ossanaTomas/CattleTracking_EmbeddedSystemsProyect/dashboard-app/images/dashboard3.png

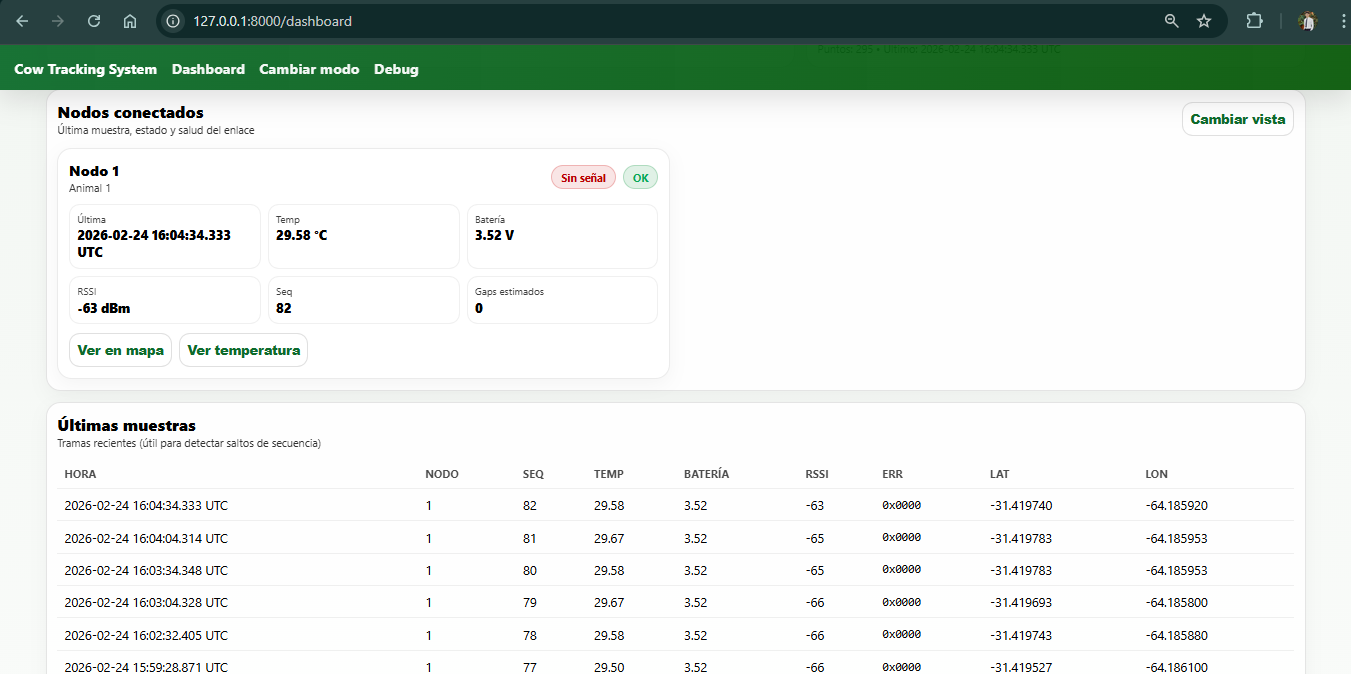
dashboard-app/images/dashboard3.png
