ossanaTomas/CattleTracking_EmbeddedSystemsProyect/dashboard-app/images/dashboard5.png

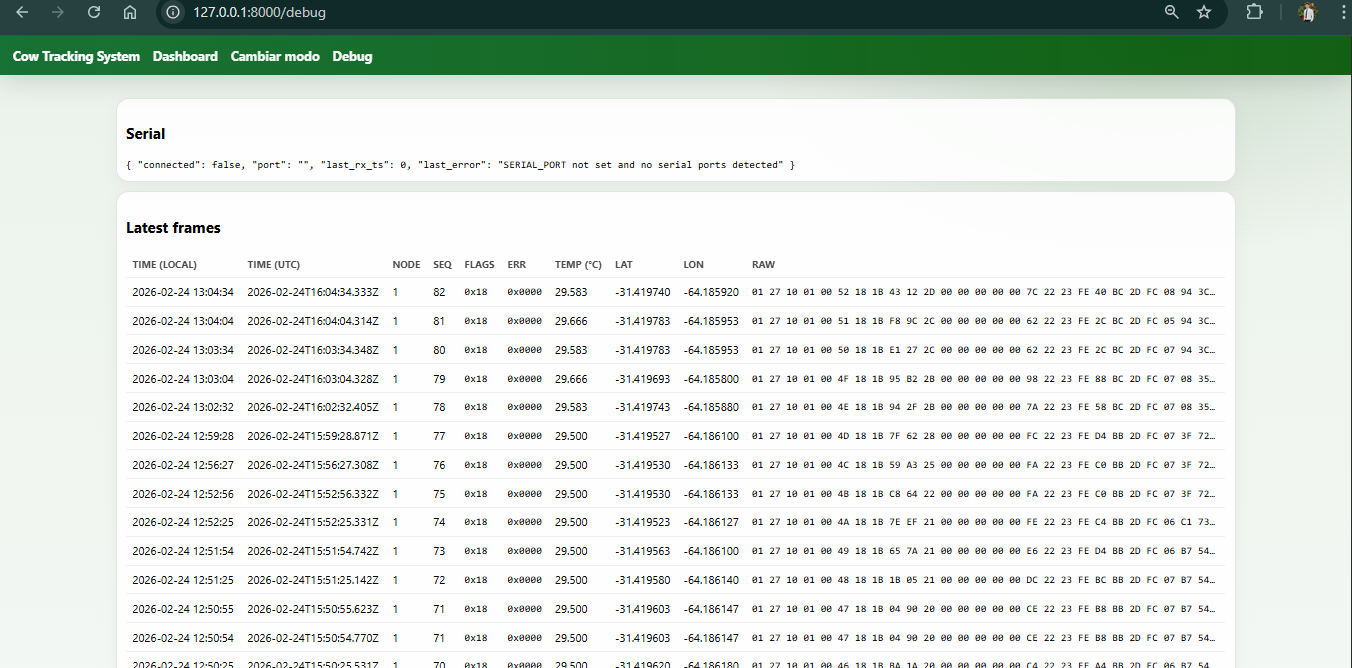
dashboard-app/images/dashboard5.png
