ossanaTomas/CattleTracking_EmbeddedSystemsProyect/firmware/firmware-tracker/Core/Src/OneWire.c

#include "OneWire.h"
#include "stm32f1xx_hal.h"
#include "stdio.h"
#include "string.h"
volatile uint8_t recvFlag;
volatile uint16_t rc_buffer[5];
int8_t Tempi[2];
/**
    @author Stanislav Lakhtin
    @date   11.07.2016
    @brief      @brief Implementación del protocolo 1wire basado en la biblioteca libopencm3 para el microcontrolador STM32F103
 	 	 	 	 	 	Quizás la biblioteca funcione correctamente en otros Reino Unido (se requiere verificación).
 	 	 	 	 	 	Es necesario realizar una verificación para garantizar que la configuración de UART/USART sea correcta para el funcionamiento.
 	 	 	 	 	 	en modo semidúplex
 	 	 	 	 	 	La idea general es utilizar hardware USART uK para simular el funcionamiento con 1 cable.
 	 	 	 	 	 	Los dispositivos se conectan al USART seleccionado al pin TX, que debe estar conectado a la línea
 	 	 	 	 	 	de alimentación con una resistencia de 4,7K.
 	 	 	 	 	 	La implementación de la biblioteca corta RX a TX dentro del Reino Unido, dejando el pin RX disponible para su uso en otras tareas.
 	 	 	 	 	 	La implementación de la biblioteca supone un posible trabajo simultáneo con ambos buses independientes y todos a la vez.
 	 	 	 	 	 	posible UART/USART en el microcontrolador. En este caso, todos los autobuses (hasta 5 unidades) serán abordados y
 	 	 	 	 	 	encuestados individualmente.
 */


extern UART_HandleTypeDef huart2;
#define ow_uart huart2
#define OW_USART USART2
#define MAXDEVICES_ON_THE_BUS 1  // cambio por uno

/*********************************************************************************************/
float Temp[MAXDEVICES_ON_THE_BUS];

uint8_t devices;
OneWire ow;
uint32_t pDelay = 300, i;
uint8_t sensor;

Temperature t;

DEVInfo devInfo;


char *crcOK;

uint16_t USART_ReceiveData(USART_TypeDef* USARTx)
{
	/* Check the parameters */
	assert_param(IS_USART_ALL_PERIPH(USARTx));

	/* Receive Data */
	return (uint16_t)(USARTx->DR & (uint16_t)0x01FF);
}

void USART_SendData(USART_TypeDef* USARTx, uint16_t Data)
{
	/* Check the parameters */
	assert_param(IS_USART_ALL_PERIPH(USARTx));
	assert_param(IS_USART_DATA(Data));

	/* Transmit Data */
	USARTx->DR = (Data & (uint16_t)0x01FF);
}


uint8_t getUsartIndex(void);

void usart_setup(uint32_t baud) {

	ow_uart.Instance = OW_USART;
	ow_uart.Init.BaudRate = baud;
	ow_uart.Init.WordLength = UART_WORDLENGTH_8B;
	ow_uart.Init.StopBits = UART_STOPBITS_1;
	ow_uart.Init.Parity = UART_PARITY_NONE;
	ow_uart.Init.Mode = UART_MODE_TX_RX;
	ow_uart.Init.HwFlowCtl = UART_HWCONTROL_NONE;
	ow_uart.Init.OverSampling = UART_OVERSAMPLING_16;
	if (HAL_HalfDuplex_Init(&ow_uart) != HAL_OK)
	{
		//	    Error_Handler();
		__asm__("NOP");
	}

	__HAL_UART_ENABLE_IT(&ow_uart, UART_IT_RXNE);
}

void owInit(OneWire *ow) {
	int i=0, k = 0;
	for (; i < MAXDEVICES_ON_THE_BUS; i++) {
		uint8_t *r = (uint8_t *)&ow->ids[i];
		k=0;
		for (; k < 8; k++)
			r[k] = 0;
	}
	k=0;
	for (; k < 8; k++)
		ow->lastROM[k] = 0x00;
	ow->lastDiscrepancy = 64;

}

void owReadHandler() { //controlador de interrupciones USART
	uint8_t index = getUsartIndex();
	/*Comprueba que hemos provocado una interrupción debido a RXNE. */
	if (((OW_USART->CR1 & USART_CR1_RXNEIE) != 0) &&
			((OW_USART->SR & UART_FLAG_RXNE) != (uint16_t)RESET)) {

		/* Recibir datos de la periferia y restablecer la bandera*/
		while ((OW_USART->SR & UART_FLAG_RXNE) == (uint16_t)RESET){;}
		rc_buffer[index] = USART_ReceiveData(OW_USART);
		recvFlag &= ~(1 << index);//restablecer la respuesta del indicador recibida después
	}
}

/** Реализация RESET на шине 1wire
 *
 * @param N usart -- выбранный для реализации 1wire usart
 * @return Возвращает 1 если на шине кто-то есть и 0 в противном случае
 */

uint16_t owResetCmd() {
	uint16_t owPresence;

	usart_setup(9600);

	owSend(0xF0); // Send RESET отправляем импуль сброса
	owPresence = owEchoRead(); // Ждём PRESENCE на шине и вовзращаем, что есть

	usart_setup(115200);// перенастраиваем скорость UART
	return owPresence;
}

uint8_t getUsartIndex() {// смотрит по номеру UART c каким будет идти работа
	//	uint8_t result;
	//	if(OW_USART==USART1)result = 0;
	//	else if (OW_USART==USART2)result = 1;
	//	else if (OW_USART==USART3)result = 2;
	return 0;
}

void owSend(uint16_t data) {
	recvFlag |= (1 << getUsartIndex());//устанавливаем флаг если попадем в обработчик прерывания там он сбросится
	USART_SendData(OW_USART, data);//отправляем данные
	while(__HAL_UART_GET_FLAG(&ow_uart, UART_FLAG_TC) == RESET);//ждем пока передача закончится
}

uint8_t owReadSlot(uint16_t data) {//читаем у нас пришла единица или ноль в ответ
	return (data == OW_READ) ? 1 : 0; //если пришло 0xFF, то бит = 1, что то другое бит = 0
}

uint16_t owEchoRead() {//
	uint8_t i = getUsartIndex();//получаем номер USART
	uint16_t pause = 1000;
	while (recvFlag & (1 << i) && pause--);// ждем пока кто-то не ответит но не больше паузы
	return rc_buffer[i];//в зависимости от используемого номера UART
}

uint8_t *byteToBits(uint8_t ow_byte, uint8_t *bits) {//разлагаем 1 байт на 8 байт ,кодируем так скасказать в посылку для 1wire
	uint8_t i;
	for (i = 0; i < 8; i++) {
		if (ow_byte & 0x01) {//если текущий бит в байте ==1 то
			*bits = WIRE_1; //заменяем на число которое при передаче по USART для 1wire будет единцией t.e 0xFF
		} else {
			*bits = WIRE_0;// тоже самое только для 0
		}
		bits++;
		ow_byte = ow_byte >> 1; //сдвигаем обработанный бит
	}
	return bits; //возвращае массив для передачи
}

/**
 * Метод пересылает последовательно 8 байт по одному на каждый бит в data
 * @param usart -- выбранный для эмуляции 1wire UART
 * @param d -- данные
 */
void owSendByte(uint8_t d) {
	uint8_t data[8];
	int i;
	byteToBits(d, data);//преобразовываем байт в биты "массив байт для  передачи UART и эмуляции 1WIRE"
	for (i = 0; i < 8; ++i) {
		owSend(data[i]);
	}
}


uint8_t bitsToByte(uint8_t *bits) {//принимает "кодированый" массив байт полученный по UART и делает из него байт))
	uint8_t target_byte, i;
	target_byte = 0;
	for (i = 0; i < 8; i++) {
		target_byte = target_byte >> 1;
		if (*bits == WIRE_1) {//если пришло  по USART 0xFF то это у нас пришла 1ца
			target_byte |= 0x80;//устанавливаем в 1 старший бит
		}
		bits++;//передвигаемся к следующему байту который является либо 0=0x00 или 1=0xFF
	}
	return target_byte; //возвращаем полученный байт
}

/* Подсчет CRC8 массива mas длиной Len */
uint8_t owCRC(uint8_t *mas, uint8_t Len) {
	uint8_t i, dat, crc, fb, st_byt;
	st_byt = 0;
	crc = 0;
	do {
		dat = mas[st_byt];
		for (i = 0; i < 8; i++) {  // счетчик битов в байте
			fb = crc ^ dat;
			fb &= 1;
			crc >>= 1;
			dat >>= 1;
			if (fb == 1) crc ^= 0x8c; // полином
		}
		st_byt++;
	} while (st_byt < Len); // счетчик байтов в массиве
	return crc;
}

uint8_t owCRC8(RomCode *rom){
	return owCRC((uint8_t*)rom, 7);
}

/*
 * return 1 if has got one more address
 * return 0 if hasn't
 * return -1 if error reading happened
 *
 * переделать на функции обратного вызова для реакции на ошибки
 */
int hasNextRom(OneWire *ow, uint8_t *ROM) {//
	uint8_t ui32BitNumber = 0;
	int zeroFork = -1;
	uint8_t i = 0;
	if (owResetCmd() == ONEWIRE_NOBODY) { //есть ли кто на шине
		return 0;
	}
	owSendByte(ONEWIRE_SEARCH);//
	do {
		uint8_t answerBit =0;
		int byteNum = ui32BitNumber / 8;
		uint8_t *current = (ROM) + byteNum;
		uint8_t cB, cmp_cB, searchDirection = 0;
		owSend(OW_READ); // чтение прямого бита
		cB = owReadSlot(owEchoRead());//ответ от датчика
		owSend(OW_READ); // чтение инверсного бита
		cmp_cB = owReadSlot(owEchoRead());//ответ от датчика
		if (cB == cmp_cB && cB == 1)//сравниваем два ответа
			return -1;//ошибка никто не ответил
		if (cB != cmp_cB) { //нормальная ситуация пришло либо 10 либо 01
			searchDirection = cB;//выбираем в каком направлении будем двигатся дальше
		} else {//колизия пришло 00 т.е текущий бит у ROM-ов разный
			if (ui32BitNumber == ow->lastDiscrepancy)//если текущая позиция колизии равна прошлой
				searchDirection = 1;//выбираем в каком направлении будем двигатся дальше
			else {
				if (ui32BitNumber > ow->lastDiscrepancy) {//если мы зашили дальше
					searchDirection = 0;//выбираем в каком направлении будем двигатся дальше
				} else {
					searchDirection = (uint8_t) ((ow->lastROM[byteNum] >> ui32BitNumber % 8) & 0x01);
				}
				if (searchDirection == 0)
					zeroFork = ui32BitNumber;//запоминаем развилку
			}
		}
		// сохраняем бит
		if (searchDirection)
			*(current) |= 1 << ui32BitNumber % 8;//выставляем бит в текущем байте байте
		answerBit = (uint8_t) ((searchDirection == 0) ? WIRE_0 : WIRE_1);// решаем кого отключить
		owSend(answerBit);//вырубаем "мешающие" устройсва
		ui32BitNumber++;//ищем следующий бит
	} while (ui32BitNumber < 64);//пока не найден весь ROM все биты
	ow->lastDiscrepancy = zeroFork;//запоминаем развилку
	for (; i < 7; i++)
		ow->lastROM[i] = ROM[i];//запоминаем последний ROM
	return ow->lastDiscrepancy > 0;
}

// Возвращает количество устройств на шине или код ошибки, если значение меньше 0
int owSearchCmd(OneWire *ow) {
	int device = 0, nextROM;
	owInit(ow);
	do {
		nextROM = hasNextRom(ow, (uint8_t*)(&ow->ids[device])); //передаем указатель на структуру куда положить след.ROM
		if (nextROM<0)
			return -1;
		device++;
	} while (nextROM && device < MAXDEVICES_ON_THE_BUS);//ищем пока кто-то есть и этих кто-то не больше дефайна
	return device;//возвращаем порядковый номер датчика (устройства) на шине
}

void owSkipRomCmd(OneWire *ow) {//отправляет команду пропуска ROM после этого следующая команда будет
	owResetCmd();                 //для всех устройств на шине
	owSendByte(ONEWIRE_SKIP_ROM);
}

void owMatchRomCmd(RomCode *rom) {//позволяет мастеру обращаться к конкретному  ведомому устройству
	int i = 0;
	owResetCmd();
	owSendByte(ONEWIRE_MATCH_ROM);//обращаемся к конкретному устройсву
	for (; i < 8; i++)
		owSendByte(*(((uint8_t *) rom) + i));//"перебираемся по структуре как по массиву" первой звездочкой получаем i тый байт из структуры
}

void owConvertTemperatureCmd(OneWire *ow, RomCode *rom) {
	owMatchRomCmd(rom);//позволяет мастеру обращаться к конкретному  ведомому устройству
	owSendByte(ONEWIRE_CONVERT_TEMPERATURE);//говорим датчику пора бы преобразовать температуру
}

/**
 * Method for reading scratchad DS18B20 OR DS18S20
 * If sensor DS18B20 then data MUST be at least 9 byte
 * If sensor DS18S20 then data MUST be at least 2 byte
 * @param ow -- OneWire pointer
 * @param rom -- selected device on the bus
 * @param data -- buffer for data
 * @return data
 */
uint8_t *owReadScratchpadCmd(OneWire *ow, RomCode *rom, uint8_t *data) {//читаем память датчика
	uint16_t b = 0, p;
	switch (rom->family) {
	case DS18B20:
	case DS18S20:
		p = 72;  //9*8 =72 == равняется 9 байт данных
		break;
	default:
		return data;

	}
	owMatchRomCmd(rom);
	owSendByte(ONEWIRE_READ_SCRATCHPAD);//отправляем команду на чтение памяти
	while (b < p) {// пока мы не обработали 9 байт
		uint8_t pos = (uint8_t) ((p - 8) / 8 - (b / 8)); //позиция обрабатываемого байта
		uint8_t bt;
		owSend(OW_READ);
		bt = owReadSlot(owEchoRead());//читаем данные
		if (bt == 1)
			data[pos] |= 1 << b % 8;//выставляем бит в нужной позиции
		else
			data[pos] &= ~(1 << b % 8);//сбрасываем бит в нужной позиции
		b++;//следующий бит
	}
	return data;
}

void owWriteDS18B20Scratchpad(OneWire *ow, RomCode *rom, uint8_t th, uint8_t tl, uint8_t conf) {
	if (rom->family != DS18B20)
		return;
	owMatchRomCmd(rom);//обращаемся к конкретному устройству
	owSendByte(ONEWIRE_WRITE_SCRATCHPAD);//будем записывать в память
	owSendByte(th);//пороги для температур
	owSendByte(tl);
	owSendByte(conf);
}

/**
 * Get last mesaured temperature from DS18B20 or DS18S20. These temperature MUST be measured in previous
 * opearions. If you want to measure new value you can set reSense in true. In this case next invocation
 * that method will return value calculated in that step.
 * @param ow -- OneWire bus pointer
 * @param rom -- selected device
 * @param reSense -- do you want resense temp for next time?
 * @return struct with data
 */
Temperature readTemperature(OneWire *ow, RomCode *rom, uint8_t reSense) {
	Scratchpad_DS18B20 *sp;
	//Scratchpad_DS18S20 *spP;
	Temperature t;
	uint8_t pad[9];
	t.inCelsus = 0x00;
	t.frac = 0x00;
	sp = (Scratchpad_DS18B20 *) &pad;
	//spP = (Scratchpad_DS18S20 *) &pad;
	switch (rom->family) {
	case DS18B20:
		owReadScratchpadCmd(ow, rom, pad);//читаем память  для DS18B20
		t.inCelsus = (int8_t) (sp->temp_msb << 4) | (sp->temp_lsb >> 4);//целая часть
		t.frac = (uint8_t) ((((sp->temp_lsb & 0x0F)) * 10) >> 4);//дробная
		break;
	/*case DS18S20:
		owReadScratchpadCmd(ow, rom, pad);//читаем память  для DS18S20
		t.inCelsus = spP->temp_lsb >> 1;
		t.frac = (uint8_t) 5 * (spP->temp_lsb & 0x01);
		break;*/
	default:
		return t;
	}
	if (reSense) {
		owConvertTemperatureCmd(ow, rom);//можно сразу после как забрали данные отдаем датчику команду на преобразования температуры
	}
	return t;
}

void owCopyScratchpadCmd(OneWire *ow, RomCode *rom) {
	owMatchRomCmd(rom);
	owSendByte(ONEWIRE_COPY_SCRATCHPAD);
}

void owRecallE2Cmd(OneWire *ow, RomCode *rom) {
	owMatchRomCmd(rom);
	owSendByte(ONEWIRE_RECALL_E2);
}


int get_ROMid (void){
	if (owResetCmd() != ONEWIRE_NOBODY) {    // is anybody on the bus?
		devices = owSearchCmd(&ow);        // obtener el ROMid de todos los dispositivos en el bus o devolver un código de error
		if (devices <= 0) {
			while (1){
				pDelay = 1000000;
				for (i = 0; i < pDelay * 1; i++)    /* Wait a bit. */
					__asm__("nop");
			}

		}
		i = 0;
		for (; i < devices; i++) {//enviar a la consola todas las ROM encontradas
			RomCode *r = &ow.ids[i];
			uint8_t crc = owCRC8(r);
			crcOK = (crc == r->crc)?"CRC OK":"CRC ERROR!";
			devInfo.device = i;

			sprintf(devInfo.info, "SN: %02X/%02X%02X%02X%02X%02X%02X/%02X", r->family, r->code[5], r->code[4], r->code[3],
					r->code[2], r->code[1], r->code[0], r->crc);

			if (crc != r->crc) {
				devInfo.device = i;
				sprintf (devInfo.info,"\n can't read cause CNC error");
			}
		}

	}
	pDelay = 1000000;
	for (i = 0; i < pDelay * 1; i++)
		__asm__("nop");

	if (strcmp(crcOK,"CRC OK") == 0) return 0;
	else return -1;
}

void get_Temperature (void)
{
	i=0;

	for (; i < devices; i++) {
		switch ((ow.ids[i]).family) {// cual es el sensor
		case DS18B20:
			// se devuelve el valor de la medicion anterior!
			t = readTemperature(&ow, &ow.ids[i], 1);
			Temp[i] = (float)(t.inCelsus*10+t.frac)/10.0;
			Tempi[0]=  (int8_t)(t.inCelsus);
			Tempi[1]= (int8_t)t.frac*10;
			break;
		/*case DS18S20:
			t = readTemperature(&ow, &ow.ids[i], 1);
			Temp[i] = (float)(t.inCelsus*10+t.frac)/10.0;
			break;*/
		case 0x00:
			break;
		default:
			// error handler
			break;
		}
	}
	//	pDelay = 4000000;
	//	for (i = 0; i < pDelay * 1; i++){}   /* Wait a bit. */
}
